lgszolnoki/EF9345-VideoCard/foto/IMG_6957.jpg

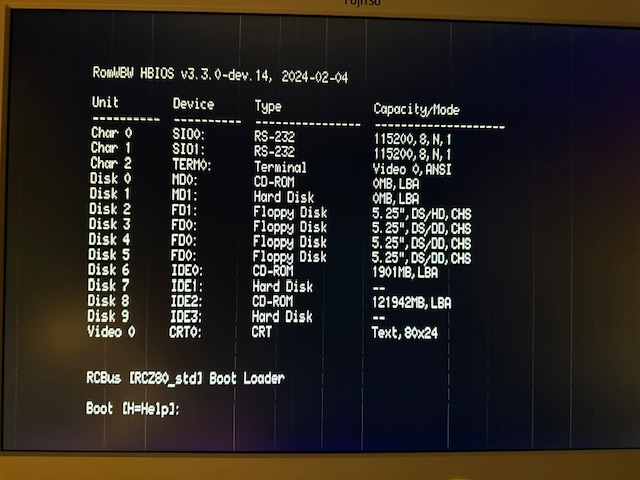
foto/IMG_6957.jpg
